JonahPi/LaserOrganizer_Make04-25/pics/IMG_9115.JPG

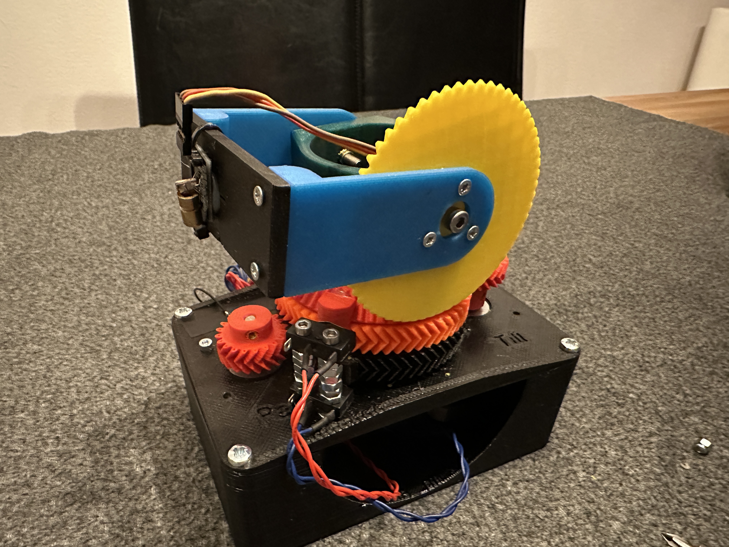
pics/IMG_9115.JPG
