JonahPi/LaserOrganizer_Make04-25/CAD/ArmGear.stl

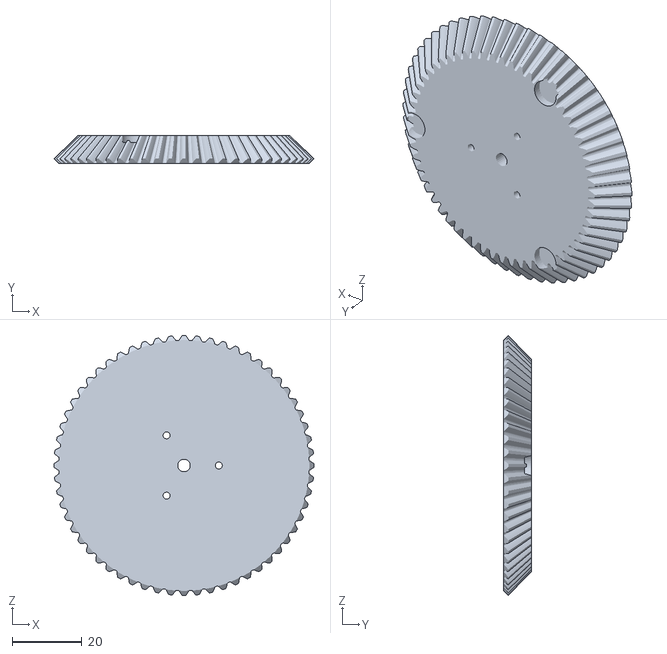
[picture p17: CAD file, 2025-06-30]
CAD/ArmGear.stl
74.7 x 8.00 x 74.7
