JonahPi/LaserOrganizer_Make04-25/src/secrets.h

#pragma once

// Wi-Fi credentials
#define WIFI_SSID "YOUR_ssid"
#define WIFI_PASSWORD "YOUR_password"

// MQTT credentials
#define MQTT_SERVER "io.adafruit.com"
#define MQTT_PORT 1883
#define MQTT_USER "YOUR_username"
#define MQTT_PASS "YOUR_mqttpassword"
#define MQTT_FEED_POSITION "YOUR_username/feeds/stepper.position"
